sekt1953/IHC-Replacement/DataSheet/Olimex/esp32-poe-dimensions.png

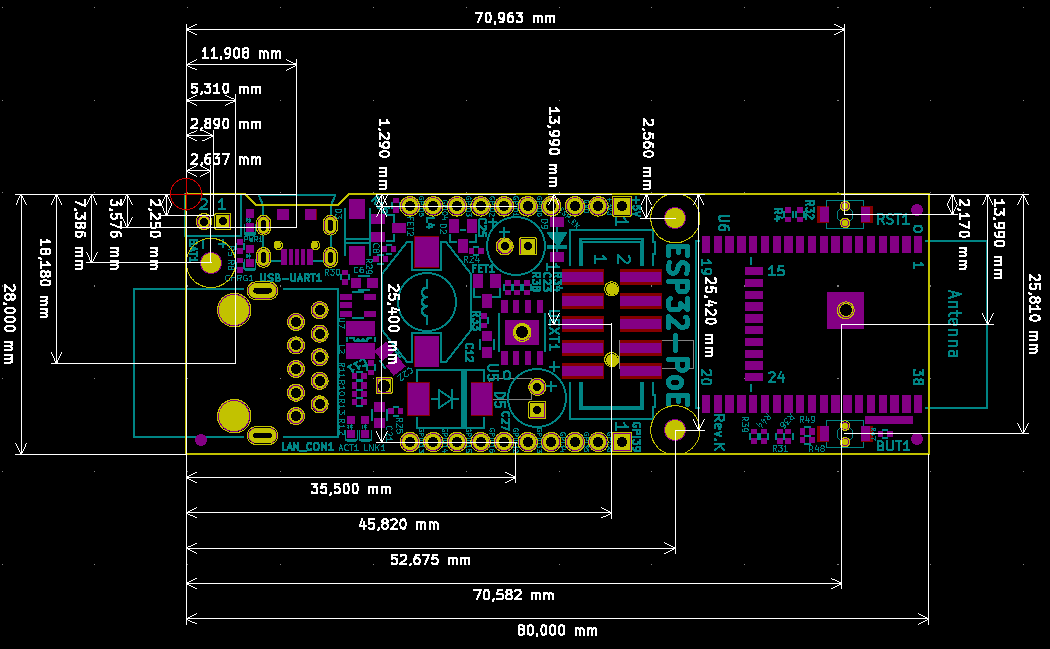
DataSheet/Olimex/esp32-poe-dimensions.png
