sekt1953/IHC-Replacement/DataSheet/Olimex/ESP32-POE_PinOut.png

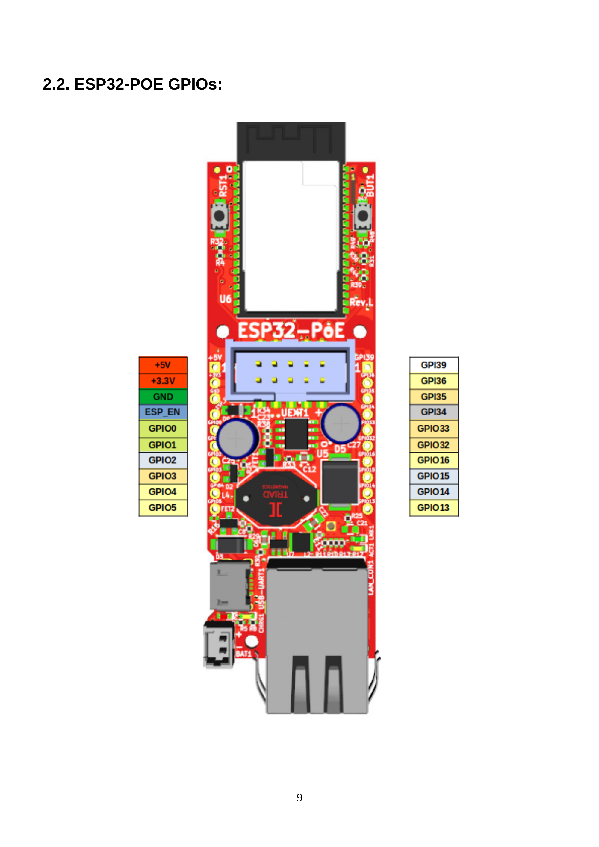
DataSheet/Olimex/ESP32-POE_PinOut.png
