sekt1953/IHC-Replacement/Doc/Images/20241107_143036.jpg

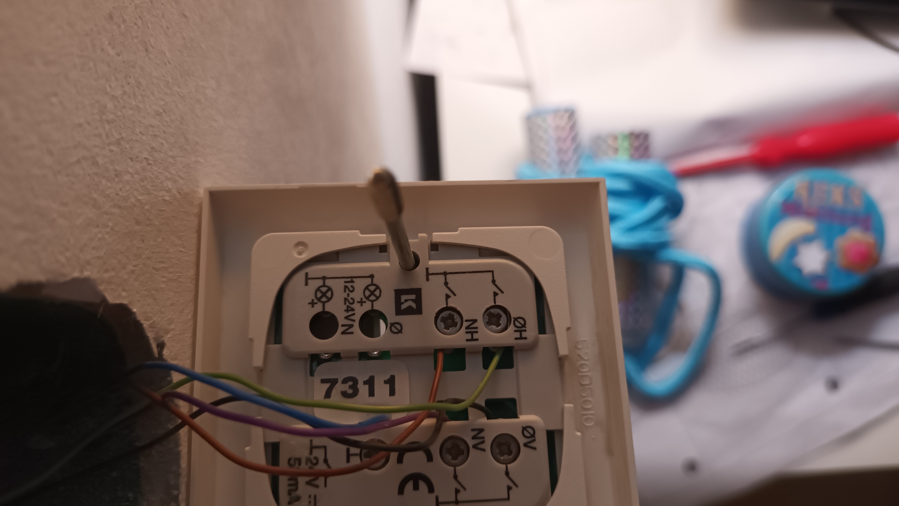
Doc/Images/20241107_143036.jpg
