sekt1953/IHC-Replacement/Doc/Images/20250314_101523.jpg

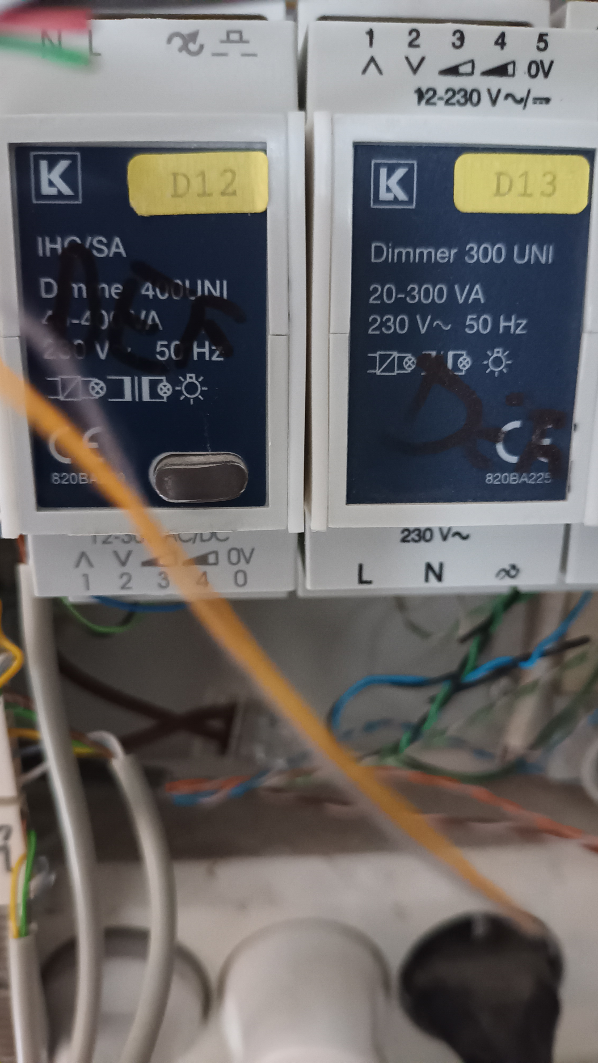
Doc/Images/20250314_101523.jpg
