sekt1953/IHC-Replacement/Doc/Images/IMG_3795.jpg

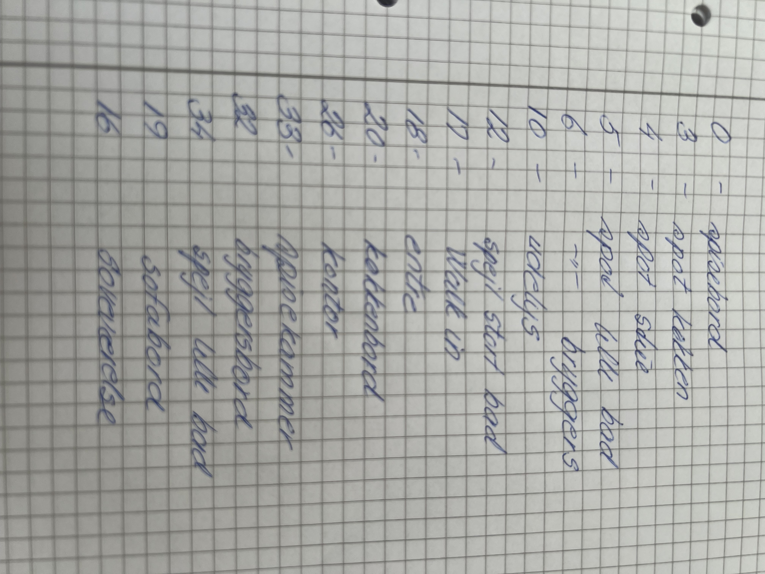
Doc/Images/IMG_3795.jpg
