sekt1953/IHC-Replacement/Doc/Images/IMG_3797.jpg

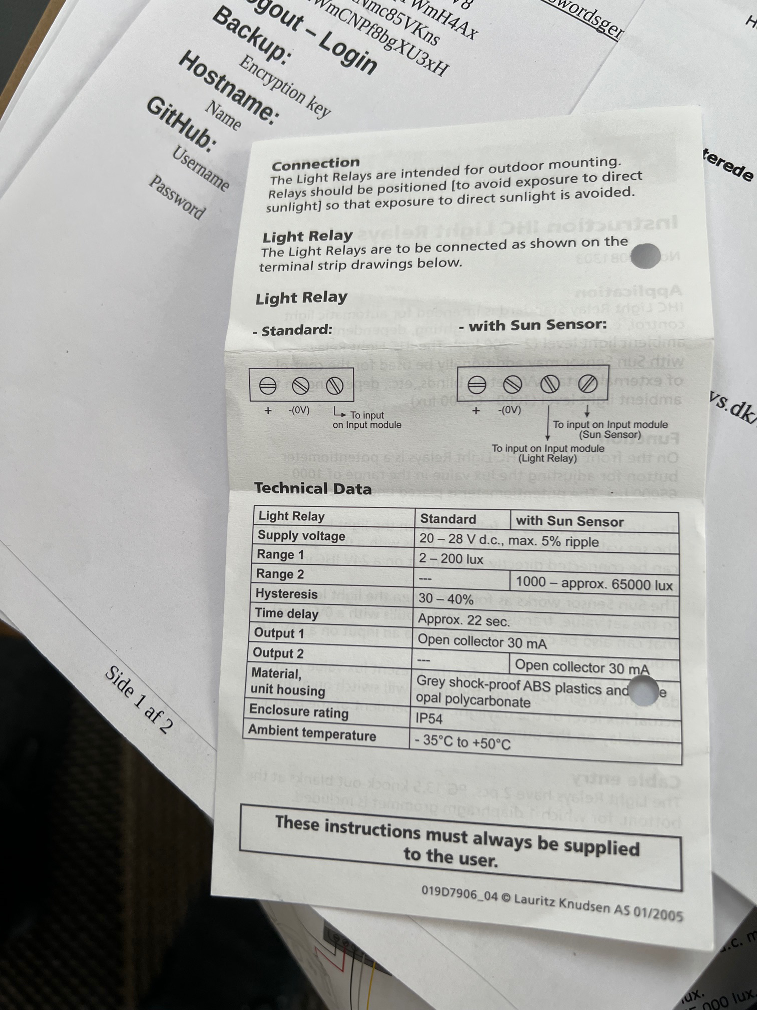
Doc/Images/IMG_3797.jpg
