sekt1953/IHC-Replacement/Doc/Images/IMG_3798.jpg

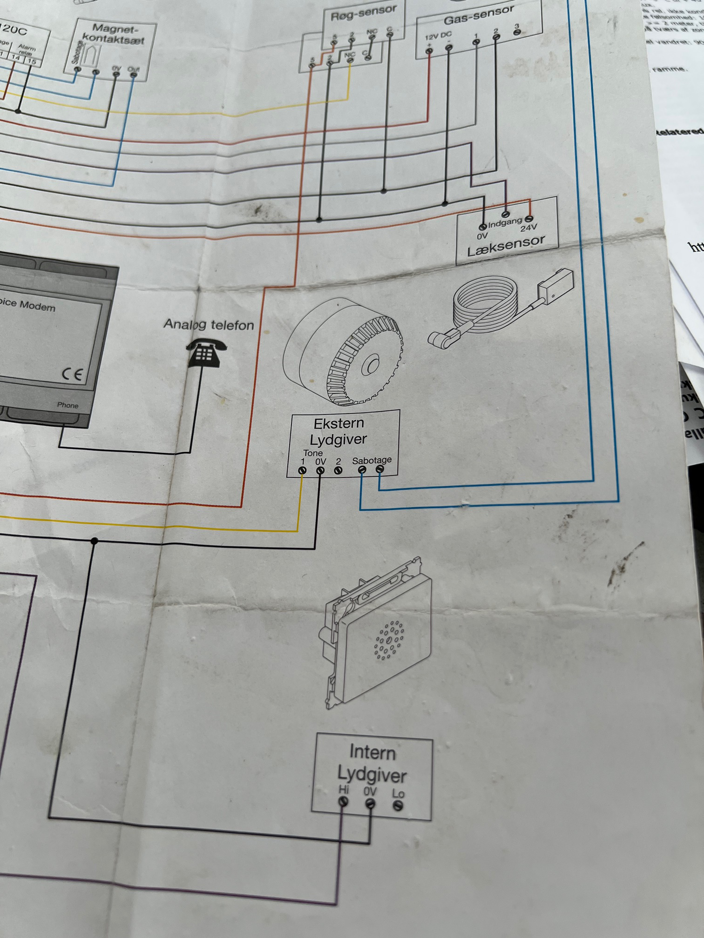
Doc/Images/IMG_3798.jpg
