sekt1953/IHC-Replacement/Doc/Images/IMG_3799.jpg

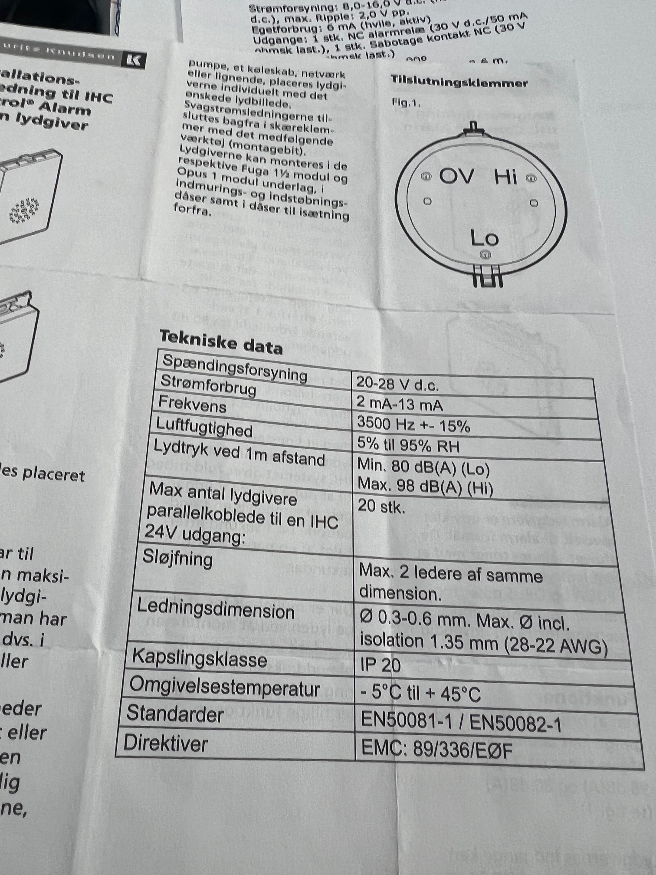
Doc/Images/IMG_3799.jpg
