sekt1953/IHC-Replacement/Doc/Images/IMG_3801.jpg

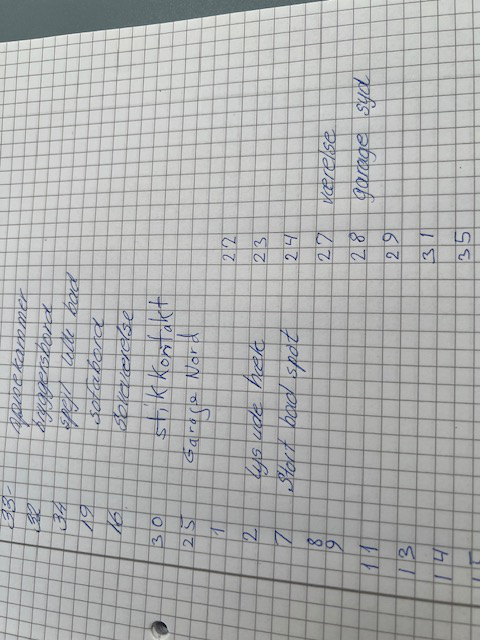
Doc/Images/IMG_3801.jpg
