sekt1953/IHC-Replacement/Doc/Images/Photos-002/20250314_101503.jpg

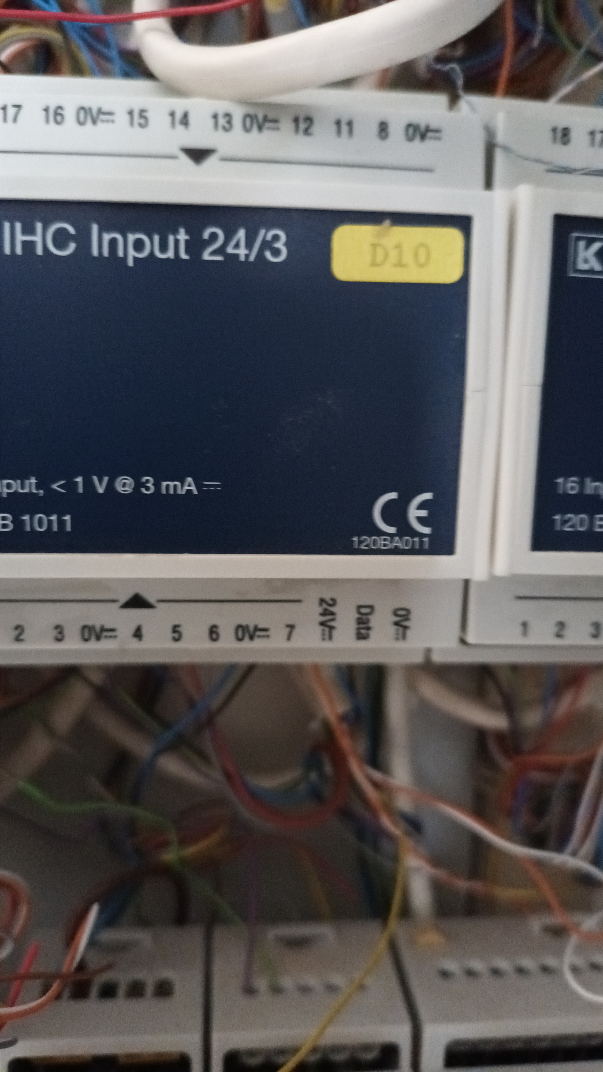
Doc/Images/Photos-002/20250314_101503.jpg
