sekt1953/IHC-Replacement/Doc/Images/Photos-002/20250314_101518.jpg

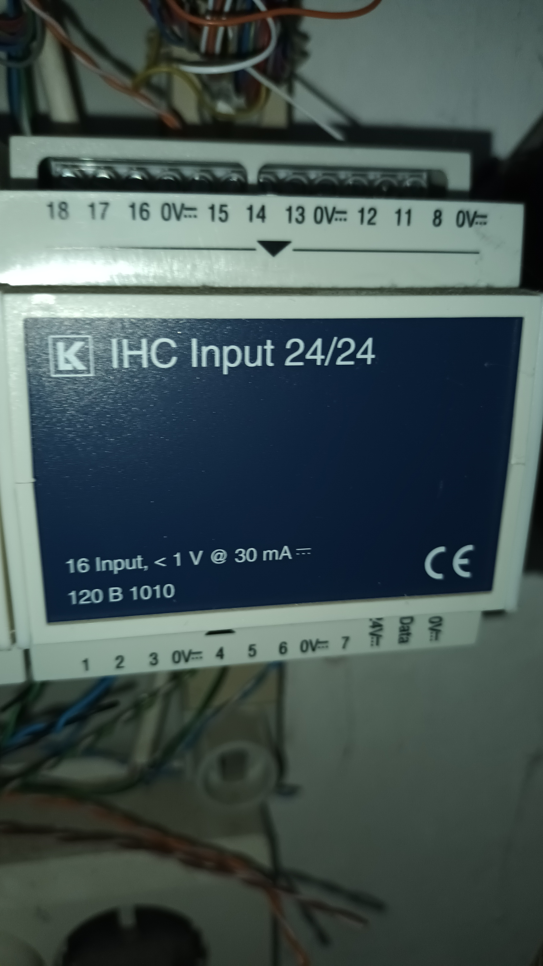
Doc/Images/Photos-002/20250314_101518.jpg
