sekt1953/IHC-Replacement/Doc/Images/Photos-003/20250314_101118.jpg

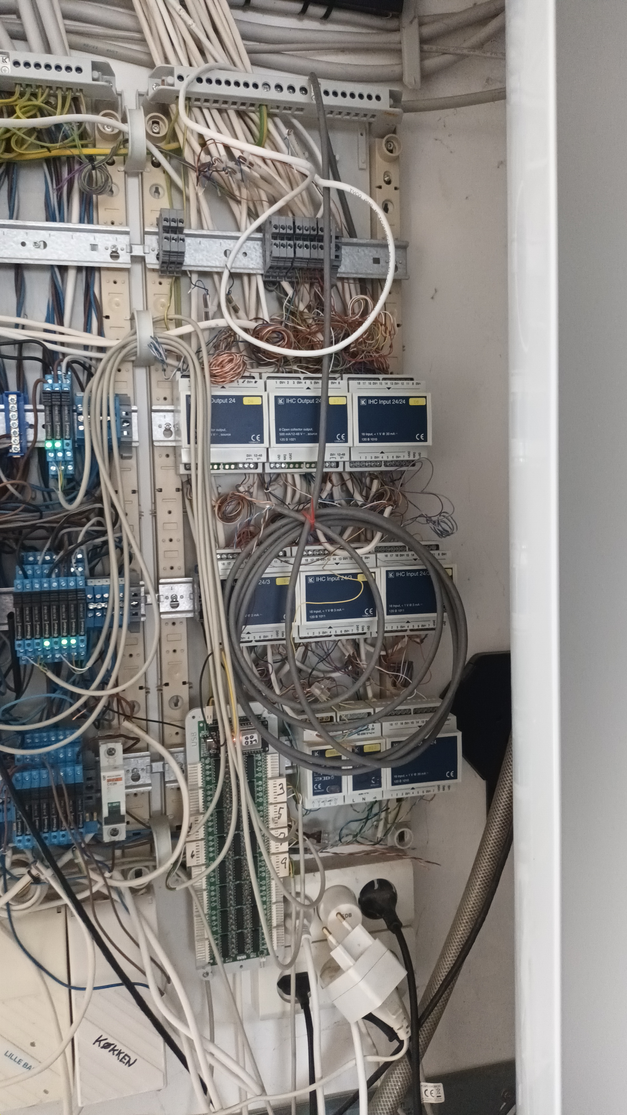
Doc/Images/Photos-003/20250314_101118.jpg
