sekt1953/IHC-Replacement/Doc/Images/Skærmbillede fra 2024-11-17 08-11-47.png

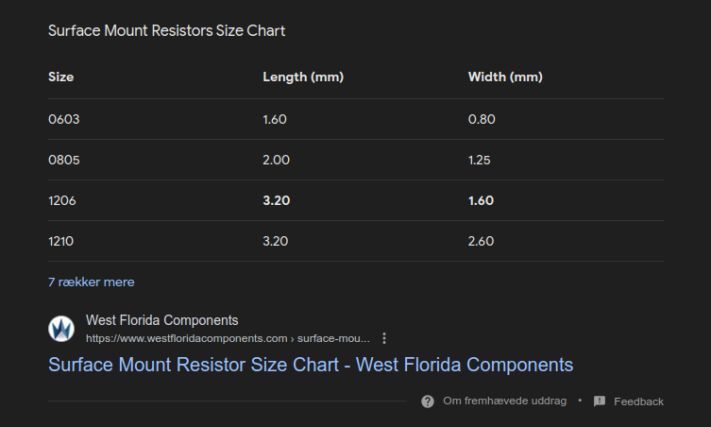
Doc/Images/Skærmbillede fra 2024-11-17 08-11-47.png
