sekt1953/IHC-Replacement/FreeCAD/Images/DinBox_100-Bottom-DimentionYZ.png

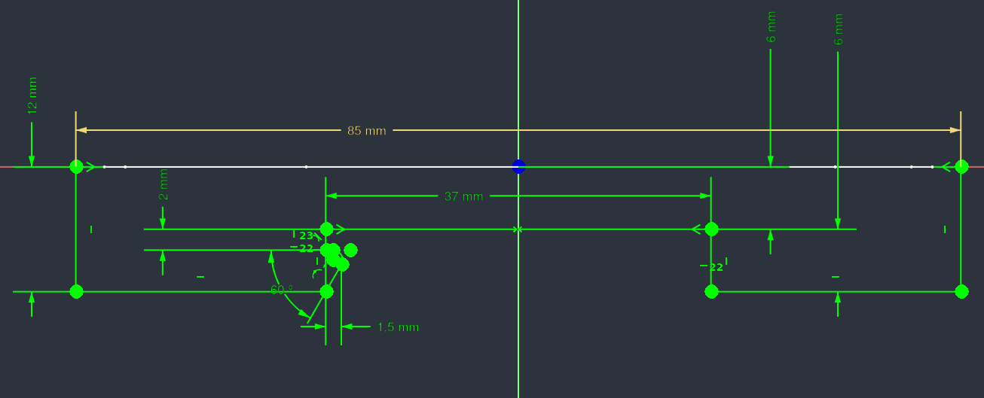
FreeCAD/Images/DinBox_100-Bottom-DimentionYZ.png
