sekt1953/IHC-Replacement/FreeCAD/Images/Skærmbillede fra 2024-12-03 21-47-26.png

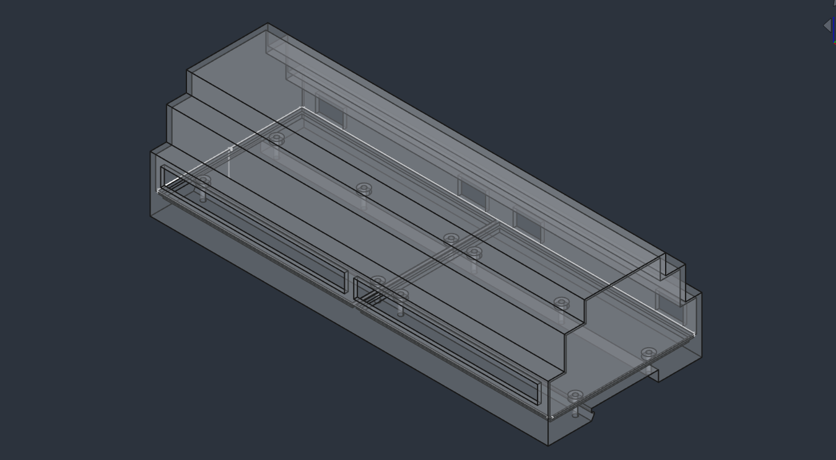
FreeCAD/Images/Skærmbillede fra 2024-12-03 21-47-26.png
