sekt1953/IHC-Replacement/FreeCAD/TrykHolder/Images/Skærmbillede fra 2025-03-21 16-08-51.png

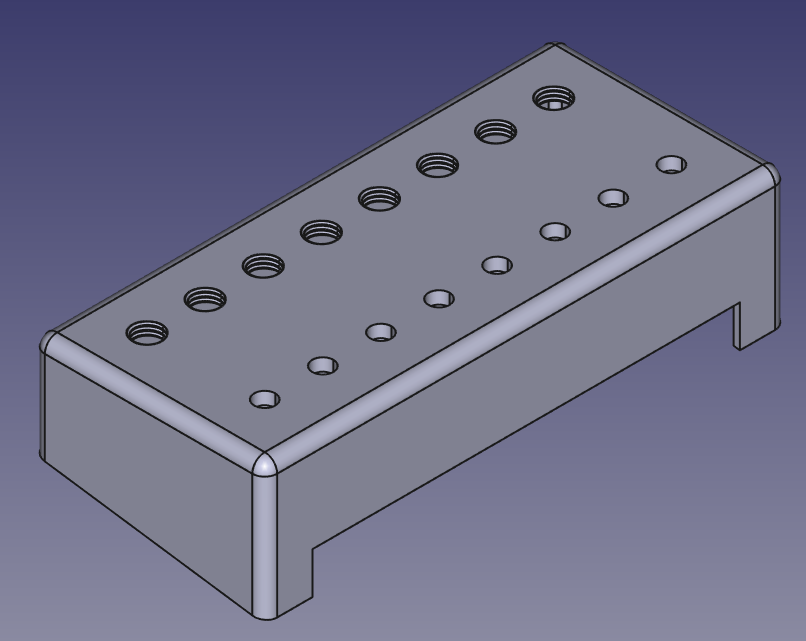
FreeCAD/TrykHolder/Images/Skærmbillede fra 2025-03-21 16-08-51.png
