sekt1953/IHC-Replacement/FreeCAD/Base-Body.3mf

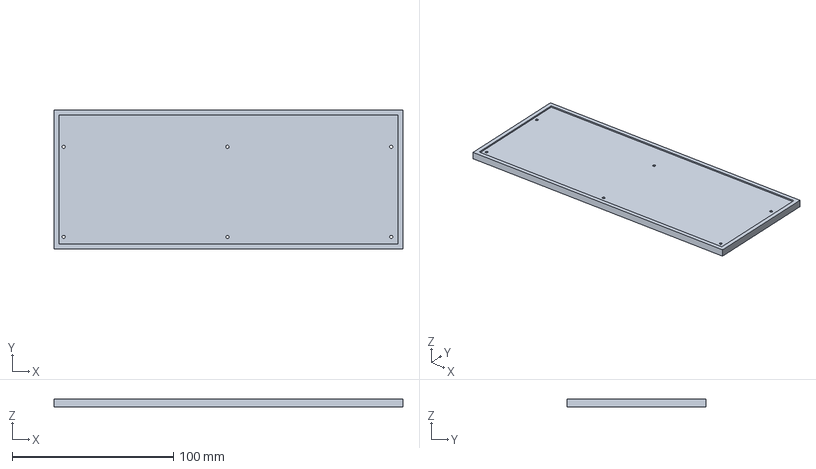
[picture p52: CAD file, 2024-11-18]
FreeCAD/Base-Body.3mf
216.5 x 86.0 x 5.00 mm
