sekt1953/IHC-Replacement/FreeCAD/DinBox/DinBox_200/Unnamed1-Body.3mf

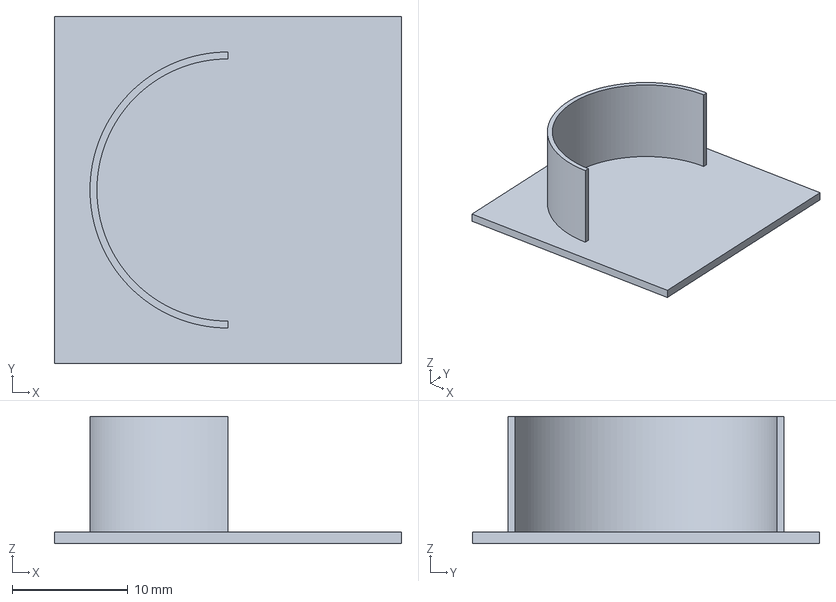
[picture p53: CAD file, 2025-04-11]
FreeCAD/DinBox/DinBox_200/Unnamed1-Body.3mf
30.0 x 30.0 x 11.0 mm
