sekt1953/IHC-Replacement/FreeCAD/Base.FCStd

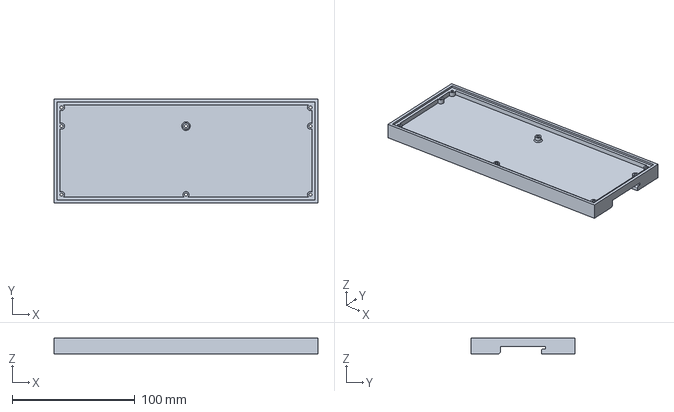
[picture p54: CAD file, 2024-11-18]
FreeCAD/Base.FCStd
215.5 x 85.0 x 12.7 mm
