sekt1953/IHC-Replacement/FreeCAD/DinBox/DinBox_200/DinBox_210-Body-Lock.3mf

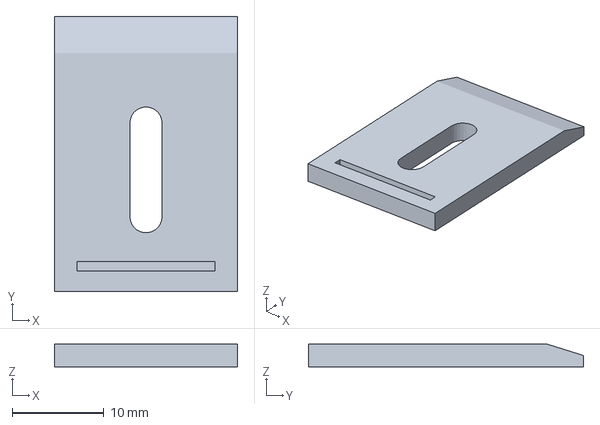
[picture p55: CAD file, 2025-04-11]
FreeCAD/DinBox/DinBox_200/DinBox_210-Body-Lock.3mf
20.0 x 30.0 x 2.50 mm
