sekt1953/IHC-Replacement/FreeCAD/DinBox/DinBox_211/DinBox_211-Body_bottomPart.3mf

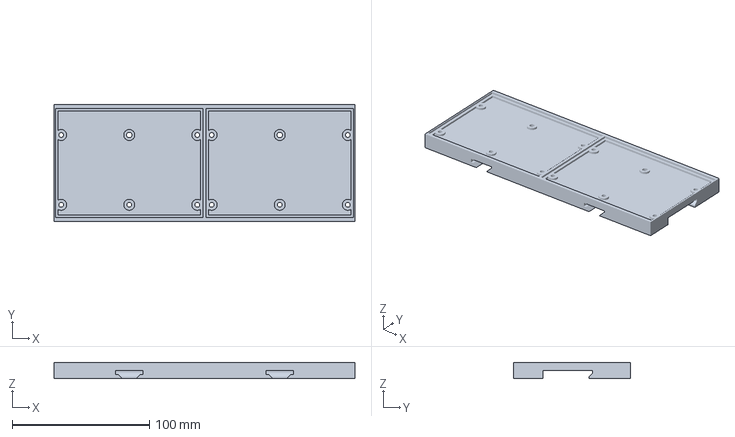
[picture p56: CAD file, 2025-04-14]
FreeCAD/DinBox/DinBox_211/DinBox_211-Body_bottomPart.3mf
219.0 x 85.0 x 12.0 mm
