sekt1953/IHC-Replacement/FreeCAD/DinBox/DinBox_200/DinBox_201-MCU.3mf

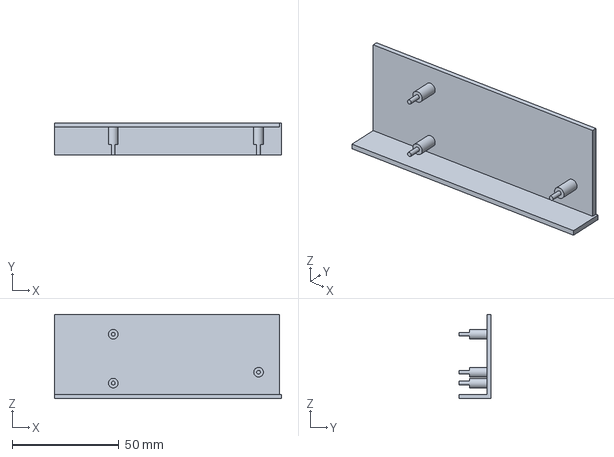
[picture p57: CAD file, 2025-04-07]
FreeCAD/DinBox/DinBox_200/DinBox_201-MCU.3mf
106.2 x 15.0 x 39.4 mm
