sekt1953/IHC-Replacement/FreeCAD/DinBox/DinBox_211/DinBox_211-Body-Lock.3mf

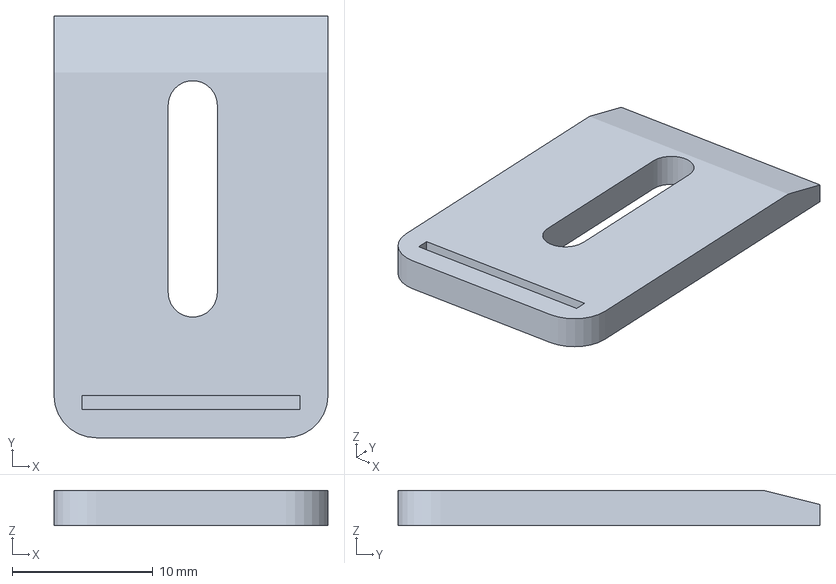
[picture p58: CAD file, 2025-04-14]
FreeCAD/DinBox/DinBox_211/DinBox_211-Body-Lock.3mf
19.5 x 30.0 x 2.50 mm
