sekt1953/IHC-Replacement/FreeCAD/DinBox/DinBox_200/DinBox_201.FCStd

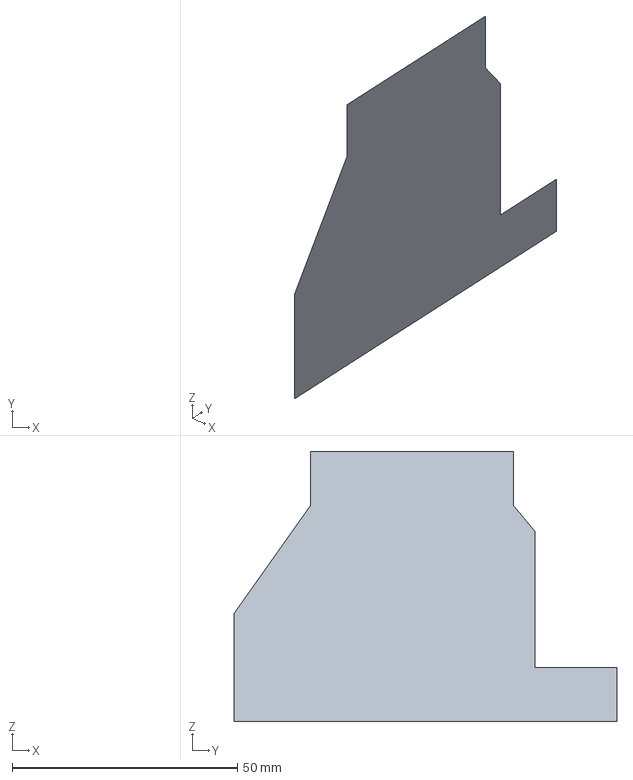
[picture p59: CAD file, 2025-04-07]
FreeCAD/DinBox/DinBox_200/DinBox_201.FCStd
0 x 85.0 x 60.0 mm
