sekt1953/IHC-Replacement/FreeCAD/DinBox/DinBox_211/DinBox_211-Body_TopPartPad005.3mf

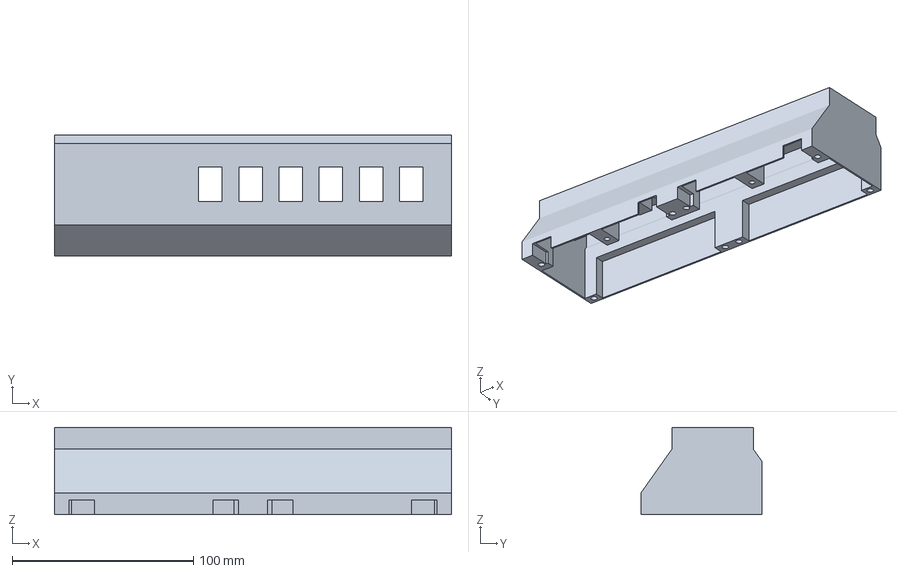
[picture p60: CAD file, 2025-04-14]
FreeCAD/DinBox/DinBox_211/DinBox_211-Body_TopPartPad005.3mf
219.0 x 66.8 x 48.0 mm
