sekt1953/IHC-Replacement/FreeCAD/DinBox/DinBox_200/DinBox_201-Body.3mf

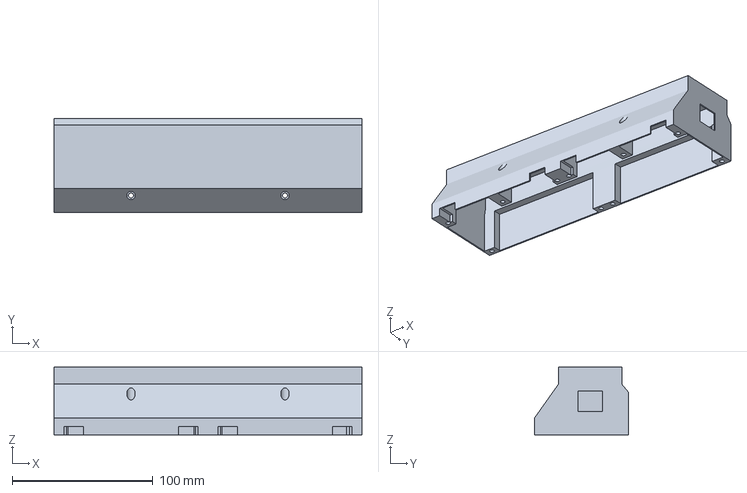
[picture p61: CAD file, 2025-04-07]
FreeCAD/DinBox/DinBox_200/DinBox_201-Body.3mf
219.0 x 66.8 x 48.0 mm
