sekt1953/IHC-Replacement/FreeCAD/DinBox/DinBox_200/DinBox_200-Top.3mf

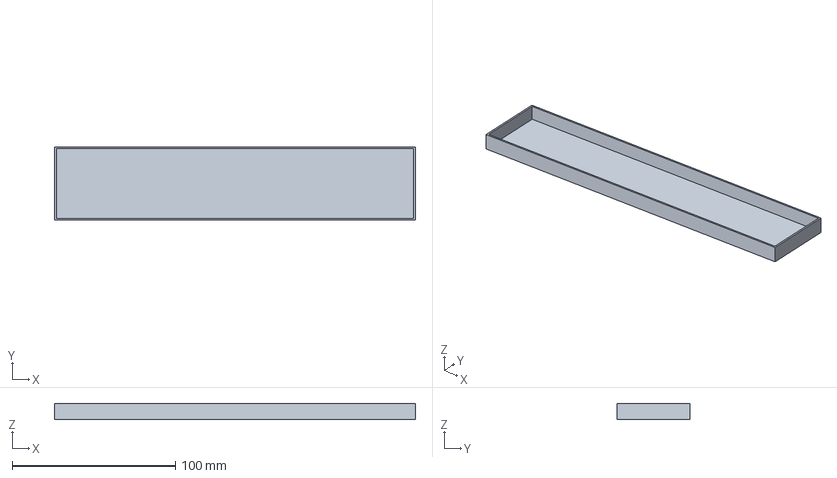
[picture p63: CAD file, 2025-04-04]
FreeCAD/DinBox/DinBox_200/DinBox_200-Top.3mf
221.4 x 45.0 x 10.0 mm
