sekt1953/IHC-Replacement/FreeCAD/DinBox/DinBox_200/DinBox_200-Body002.3mf

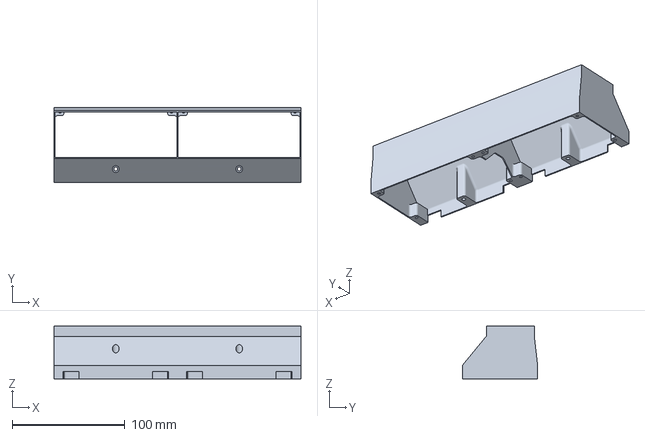
[picture p64: CAD file, 2025-04-04]
FreeCAD/DinBox/DinBox_200/DinBox_200-Body002.3mf
219.0 x 66.8 x 46.8 mm
